declanshanaghy/AlcoTop/eagleUp/eagleUp_AlcoTop_bottom.png

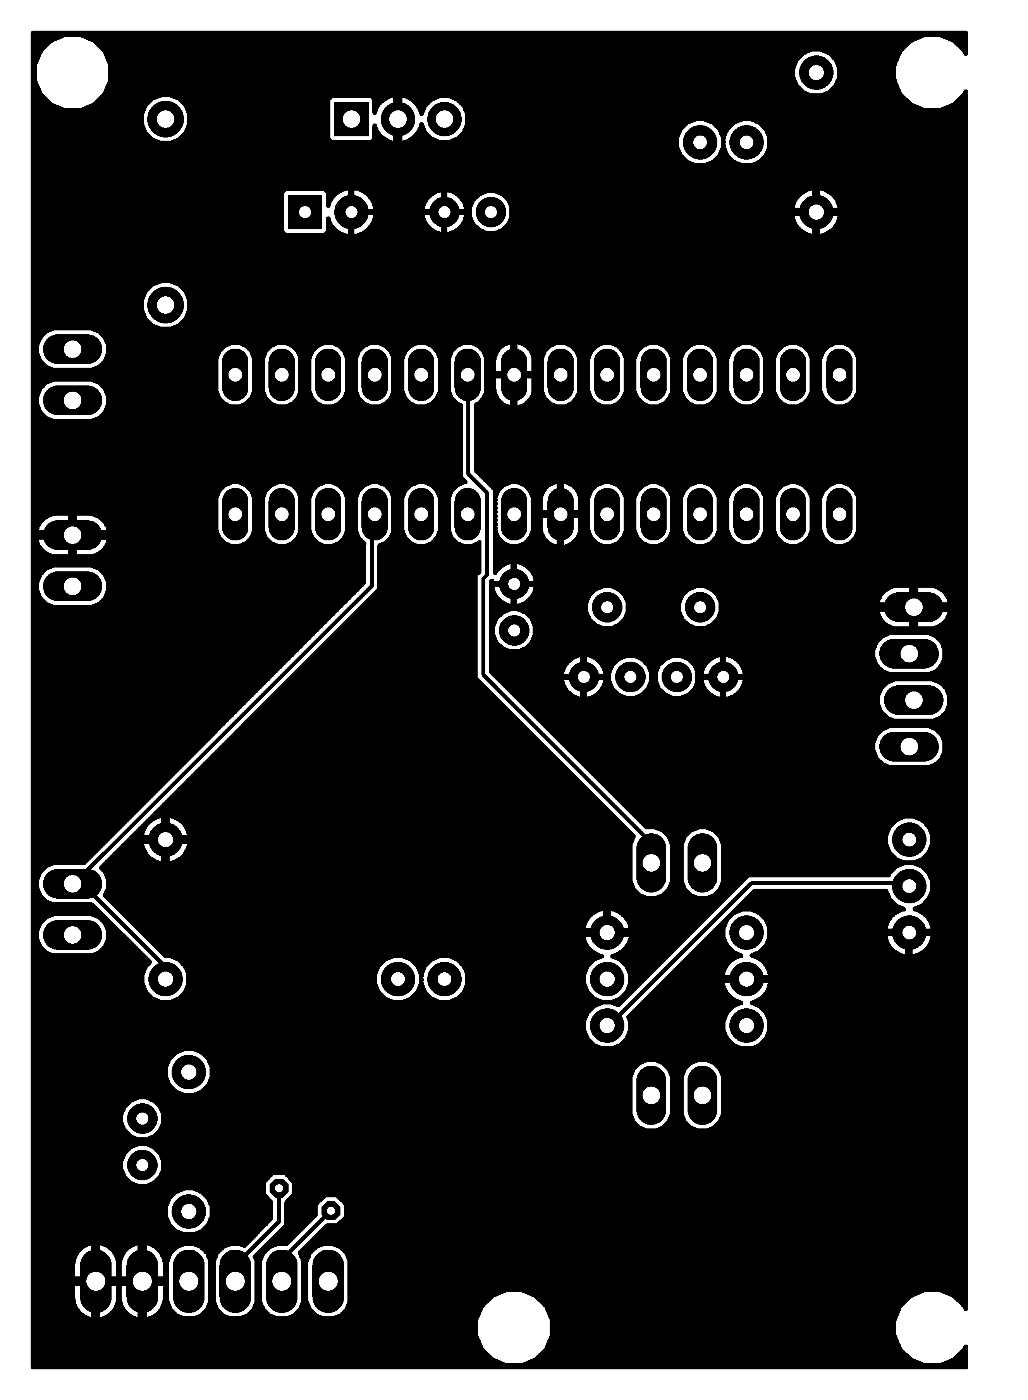
eagleUp/eagleUp_AlcoTop_bottom.png
