declanshanaghy/AlcoTop/eagleUp/eagleUp_AlcoTop_bottom_silk.png

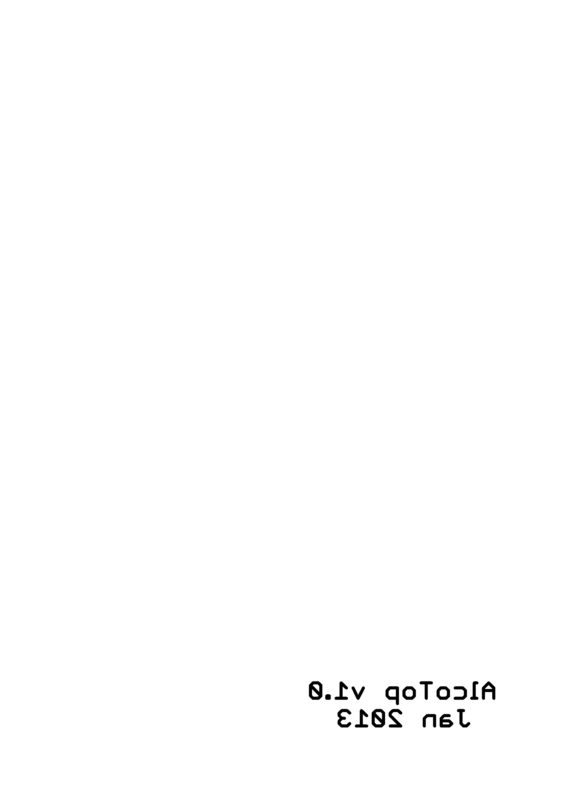
eagleUp/eagleUp_AlcoTop_bottom_silk.png
