declanshanaghy/AlcoTop/eagleUp/eagleUp_AlcoTop_imagesize.png

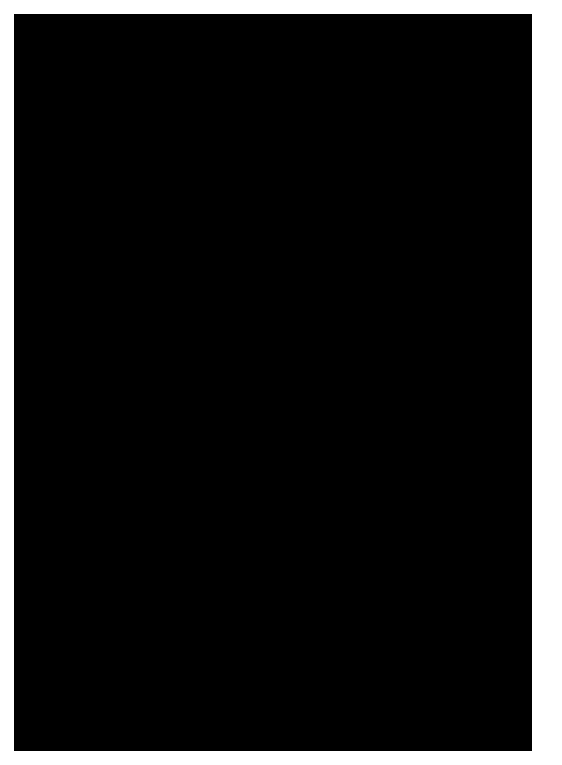
eagleUp/eagleUp_AlcoTop_imagesize.png
