declanshanaghy/AlcoTop/eagleUp/eagleUp_AlcoTop_top.png

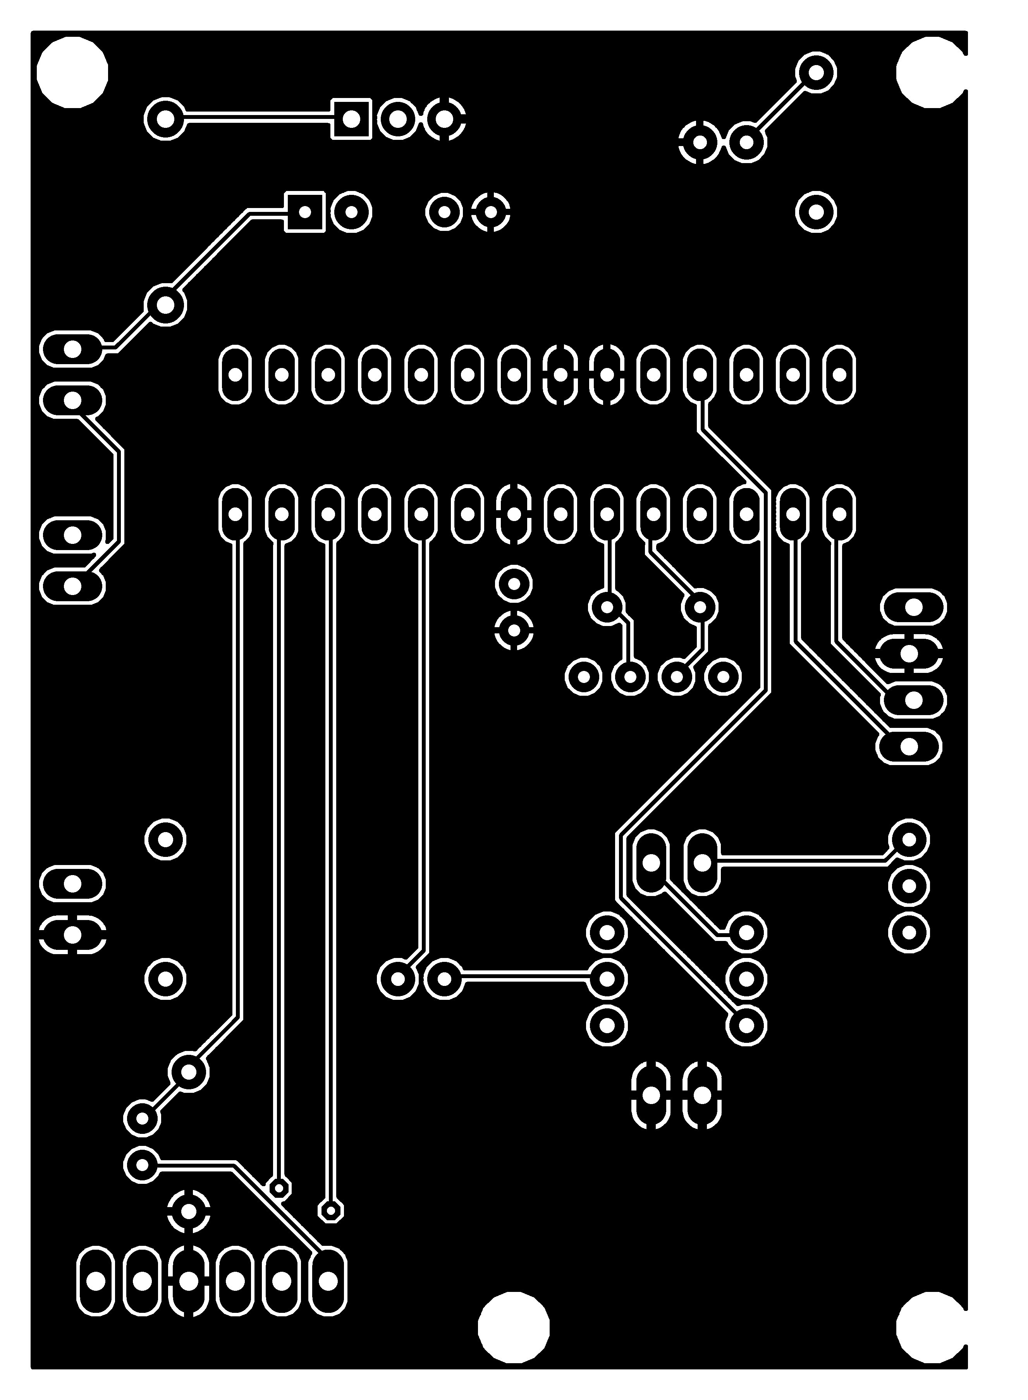
eagleUp/eagleUp_AlcoTop_top.png
